Eldalote/Drone-Project-All/PCBs/Drone main board/Documentation/Functional Diagram.png

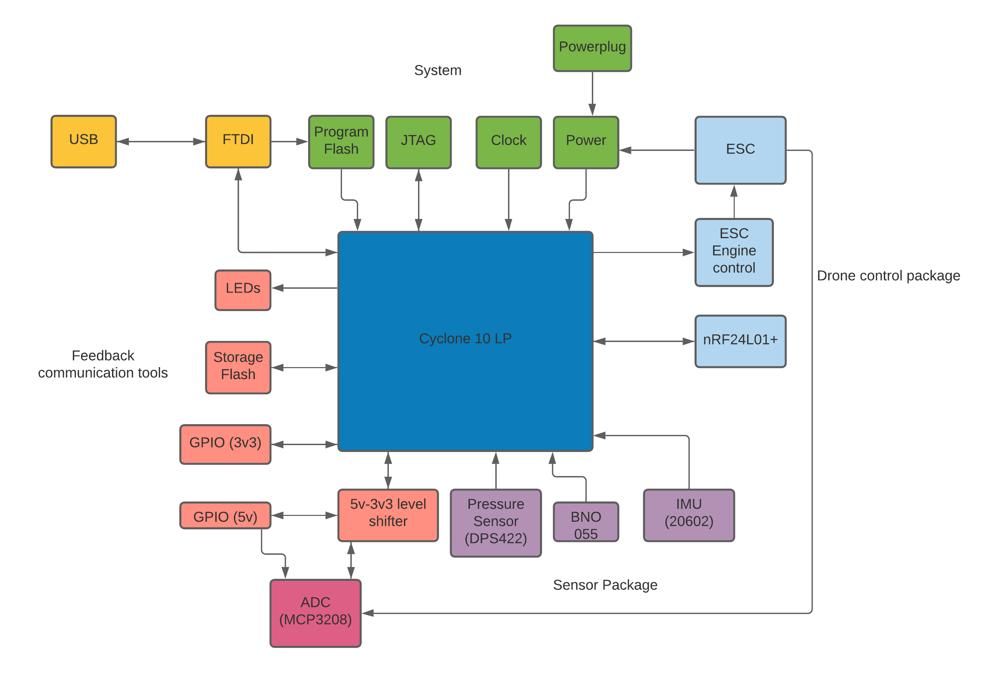
PCBs/Drone main board/Documentation/Functional Diagram.png
