Eldalote/Drone-Project-All/PCBs/Drone main board/Documentation/Pin listing/GPIOs.png

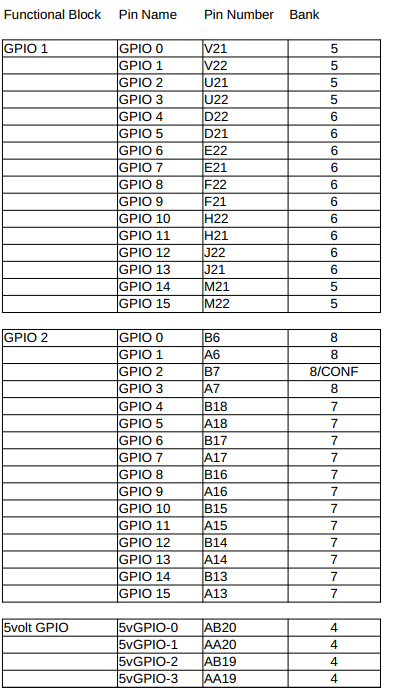
PCBs/Drone main board/Documentation/Pin listing/GPIOs.png
