Eldalote/Drone-Project-All/PCBs/Remote/CenterBoard/Documentation/Pinning by function.png

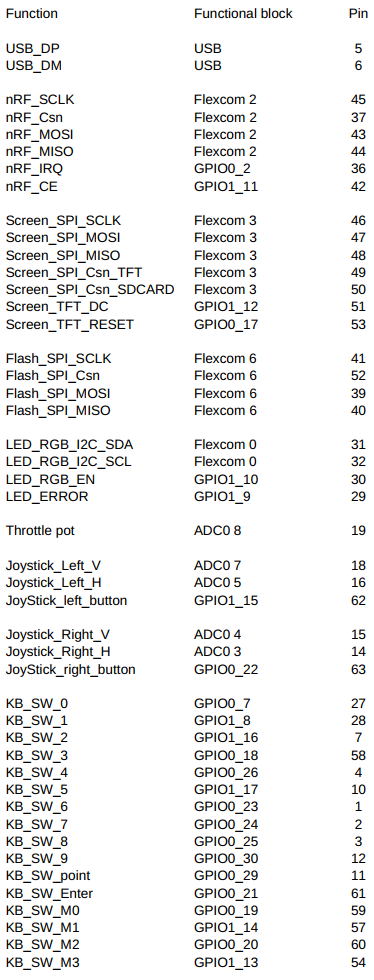
PCBs/Remote/CenterBoard/Documentation/Pinning by function.png
